netceteragroup/pulse-eco-devices/skopjepulse-v1-lorawan/firmware/skopjepulse-v1/rn2483.h

/*
 * A library for controlling a Microchip RN2483 LoRa radio.
 *
 * @Author JP Meijers
 * @Date 18/12/2015
 * @ModifiedBy hsilomedus
 *
 */

#ifndef rn2483_h
#define rn2483_h

#include "Arduino.h"
#include <SoftwareSerial.h>

class rn2483
{
  public:
    /*
     * A simplified constructor taking only a SoftwareSerial object.
     * It is assumed that LoRa WAN will be used.
     * The serial port should already be initialised when initialising this library.
     */
    rn2483(SoftwareSerial& serial);

//    /*
//     * A simplified constructor taking only a HardwareSerial object.
//     * It is assumed that LoRa WAN will be used.
//     * The serial port should already be initialised when initialising this library.
//     */
//    rn2483(HardwareSerial& serial);

    /*
     * Transmit the correct sequence to the rn2483 to trigger its autobauding feature.
     * After this operation the rn2483 should communicate at the same baud rate than us.
     */
    void autobaud();

    /*
     * Get the hardware EUI of the radio, so that we can register it on The Things Network
     * and obtain the correct AppKey.
     * You have to have a working serial connection to the radio before calling this function.
     * In other words you have to at least call autobaud() some time before this function.
     */
    String hweui();

    /*
     * Get the RN2483's version number.
     */
    String sysver();

    /*
     * Initialise the RN2483 and join the LoRa network (if applicable).
     */
    void init();

    /*
     * Initialise the RN2483 and join The Things Network using personalization.
     * This ignores your previous choice to use or not use the LoRa WAN.
     */
    void init(String* AppEUI, String* NwkSKey, String* AppSKey, String* addr, int dataRate);

//    /*
//     * Initialise the RN2483 and join The Things Network using over the air activation.
//     * This ignores your previous choice to use or not use the LoRa WAN.
//     */
//    void init(String AppEUI, String AppKey);

    /*
     * Transmit the provided data. The data is hex-encoded by this library,
     * so plain text can be provided.
     * This function is an alias for txUncnf().
     */
    void tx(byte bytes[], int length);
//
//    /*
//     * Do a confirmed transmission via LoRa WAN.
//     * Note: Only use this function if LoRa WAN is used.
//     */
//    void txCnf(byte bytes[], int length);

    /*
     * Do an unconfirmed transmission via LoRa WAN.
     * Note: Only use this function if either LoRa WAN or TTN is used.
     */
    void txUncnf(byte bytes[], int length);



  private:
    Stream& _serial;

    //Flags to switch code paths. Default is to use WAN (join OTAA)
    bool _otaa = true;

    //The default address to use on TTN if no address is defined.
    //This one falls in the "testing" address space.
    String* _devAddr;

    //the appeui to use for LoRa WAN
    String* _appeui;

    //the nwkskey to use for LoRa WAN
    String* _nwkskey;

    //the appskey to use for LoRa WAN
    String* _appskey;

    //The datarate to use for LoRa WAN
    int _dataRate;

    bool txData(String, byte bytes[], int length);

    void sendEncoded(byte bytes[], int length);

    void readreplyResponse();
//    String base16encode(String);
//    String base16decode(String);
};

#endif
